rryske2001/modul-systemowy/plytki/wersja_ostateczna_wyswietlacz_pcf_v1/plots/LCD_PCF_v4__opis.pdf

# 47n C1 E J5

J12 | A⁰ | þÿZBcze LCD

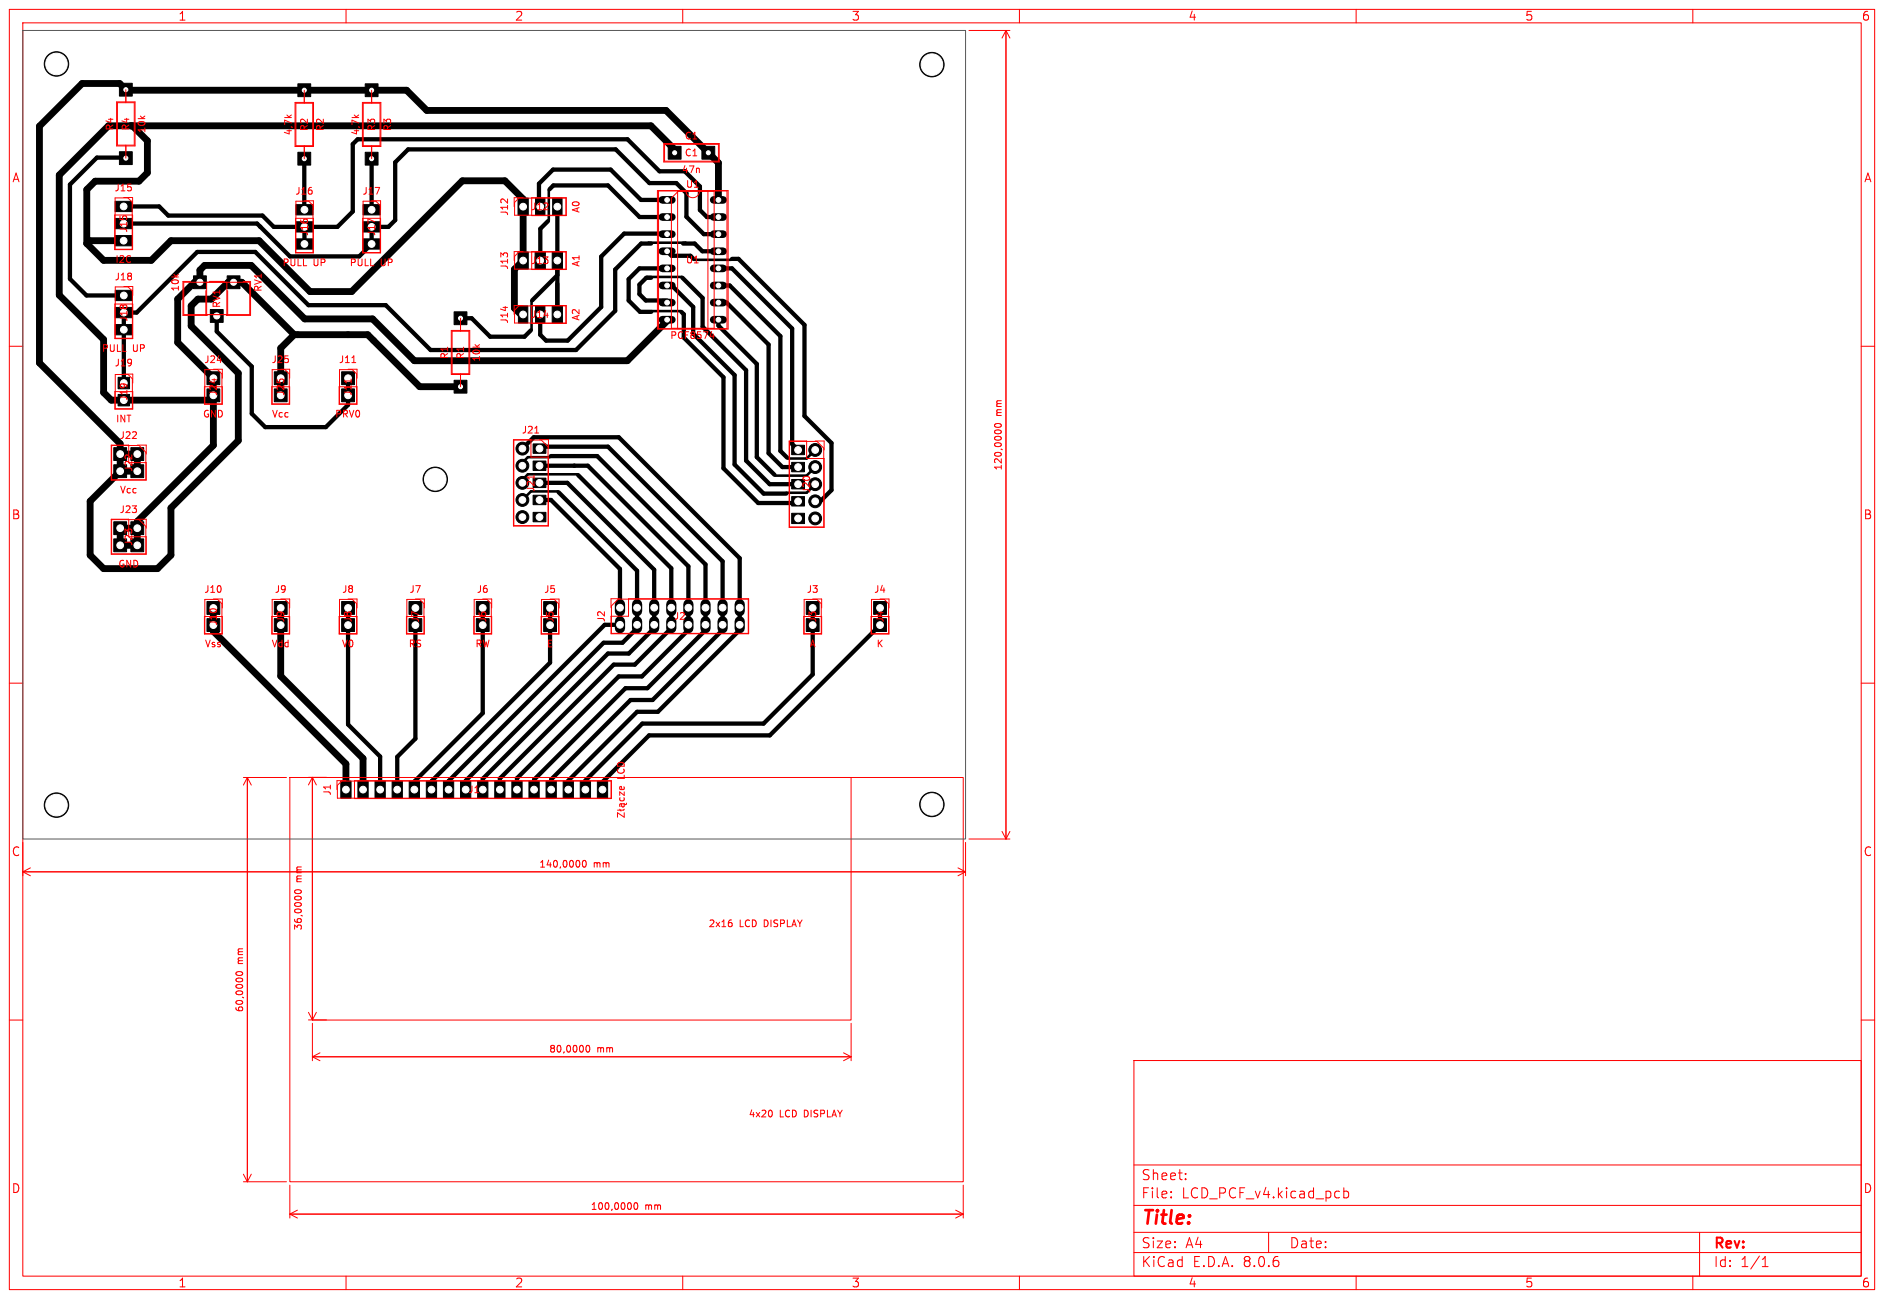
[picture p13: page 1]

Id: 1/1 Title: File: LCD_PCF_v4.kicad_pcb Sheet:
