rryske2001/modul-systemowy/plytki/wersja_ostateczna_wyswietlacz_pcf_v1/plots/wersja_ostateczna_wyswietlacz_pcf_v1_opis_sciezki.pdf

1 | 2 | 3 | 4 | 5 | 6

A

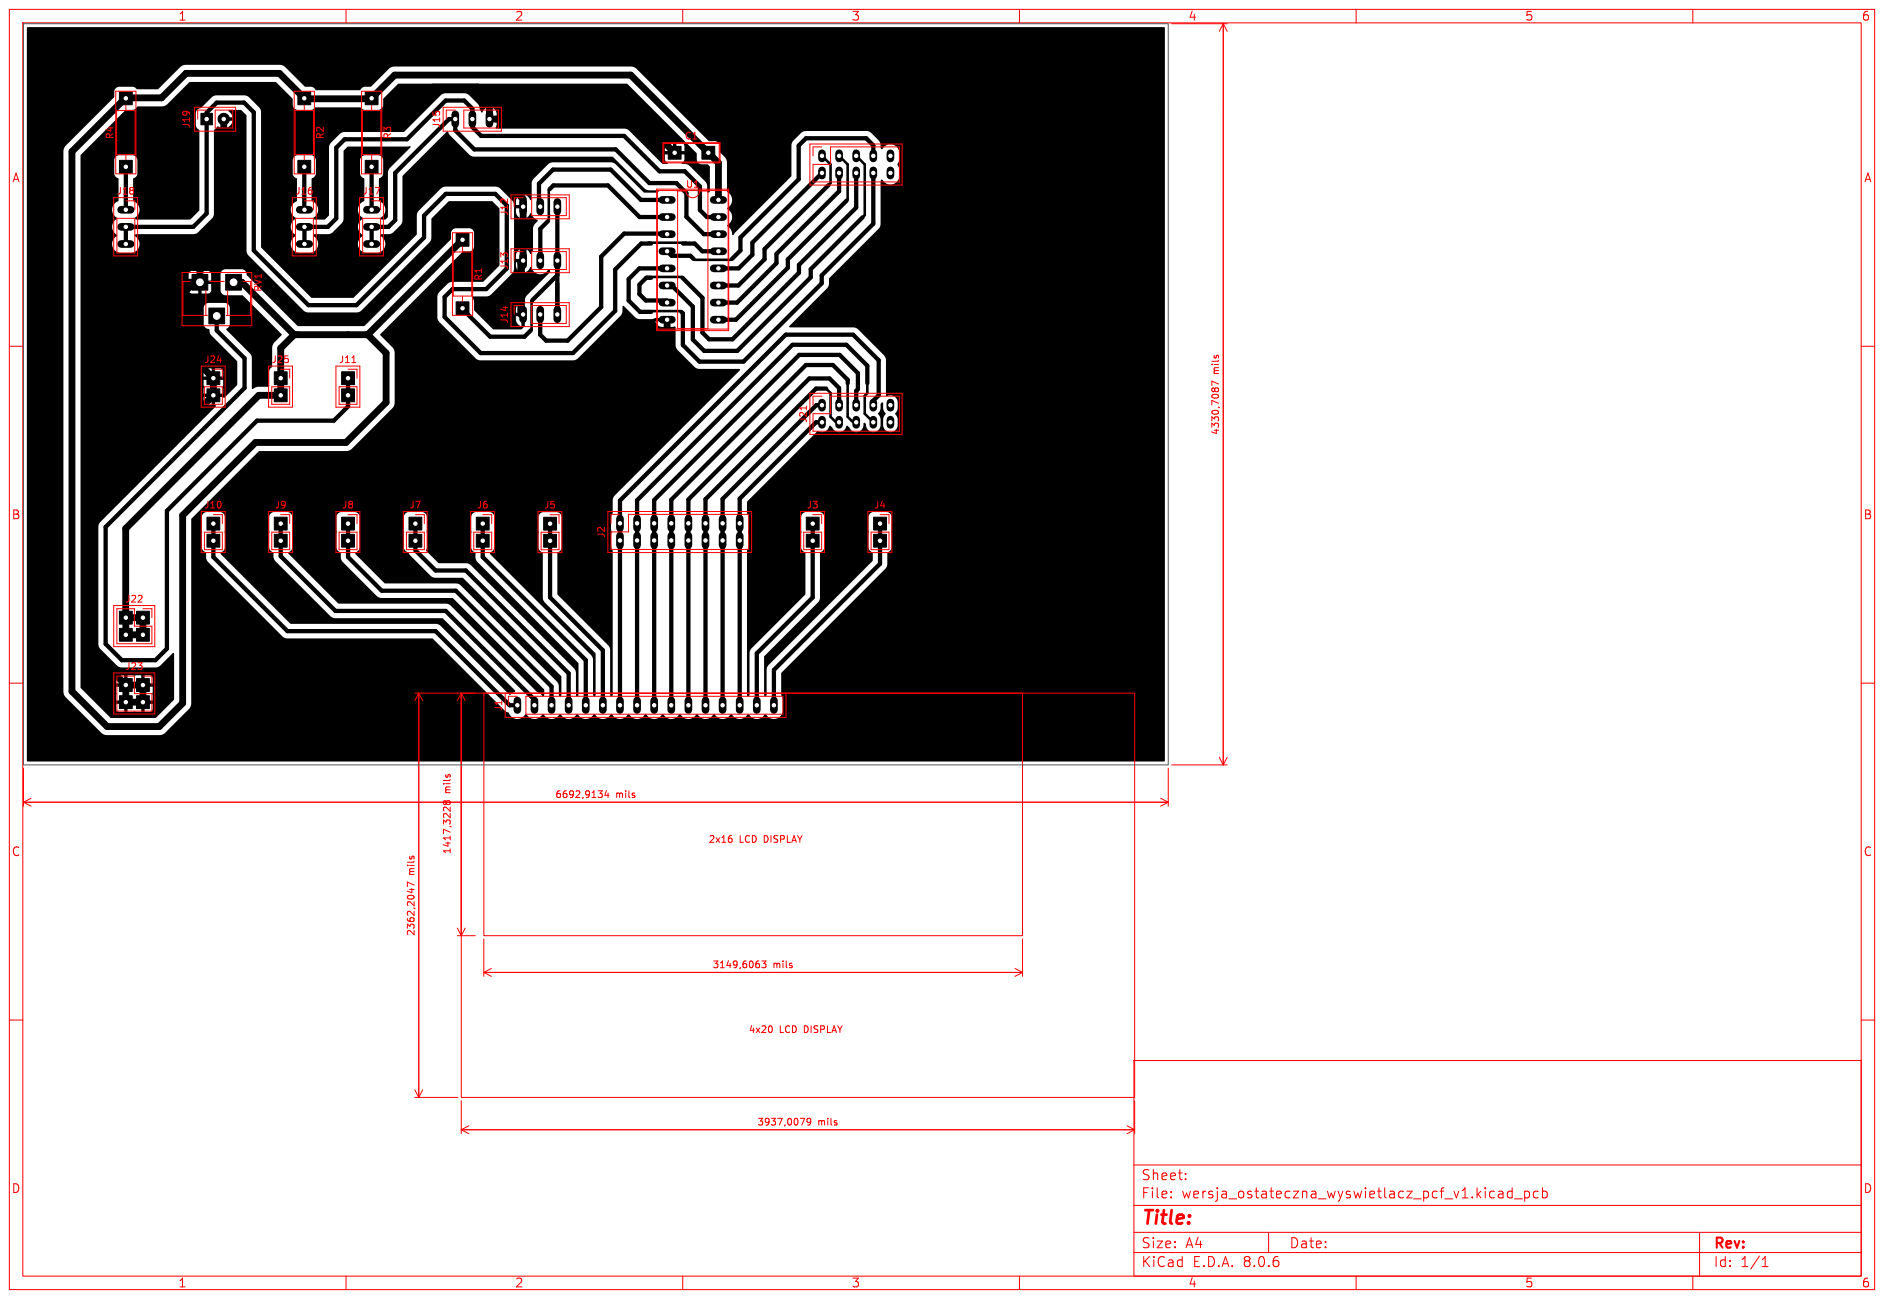
[picture p14: page 1]

Id: 1/1 Title: File: wersja_ostateczna_wyswietlacz_pcf_v1.kicad_pcb Sheet: ⁴x20 LCD DISPLAY
