rryske2001/modul-systemowy/plytki/wersja_ostateczna_wyswietlacz_pcf_v1/plots/wersja_ostateczna_wyswietlacz_pcf_v1_sciezki2.pdf

# J23 R⁴

J8 | R³ | R¹

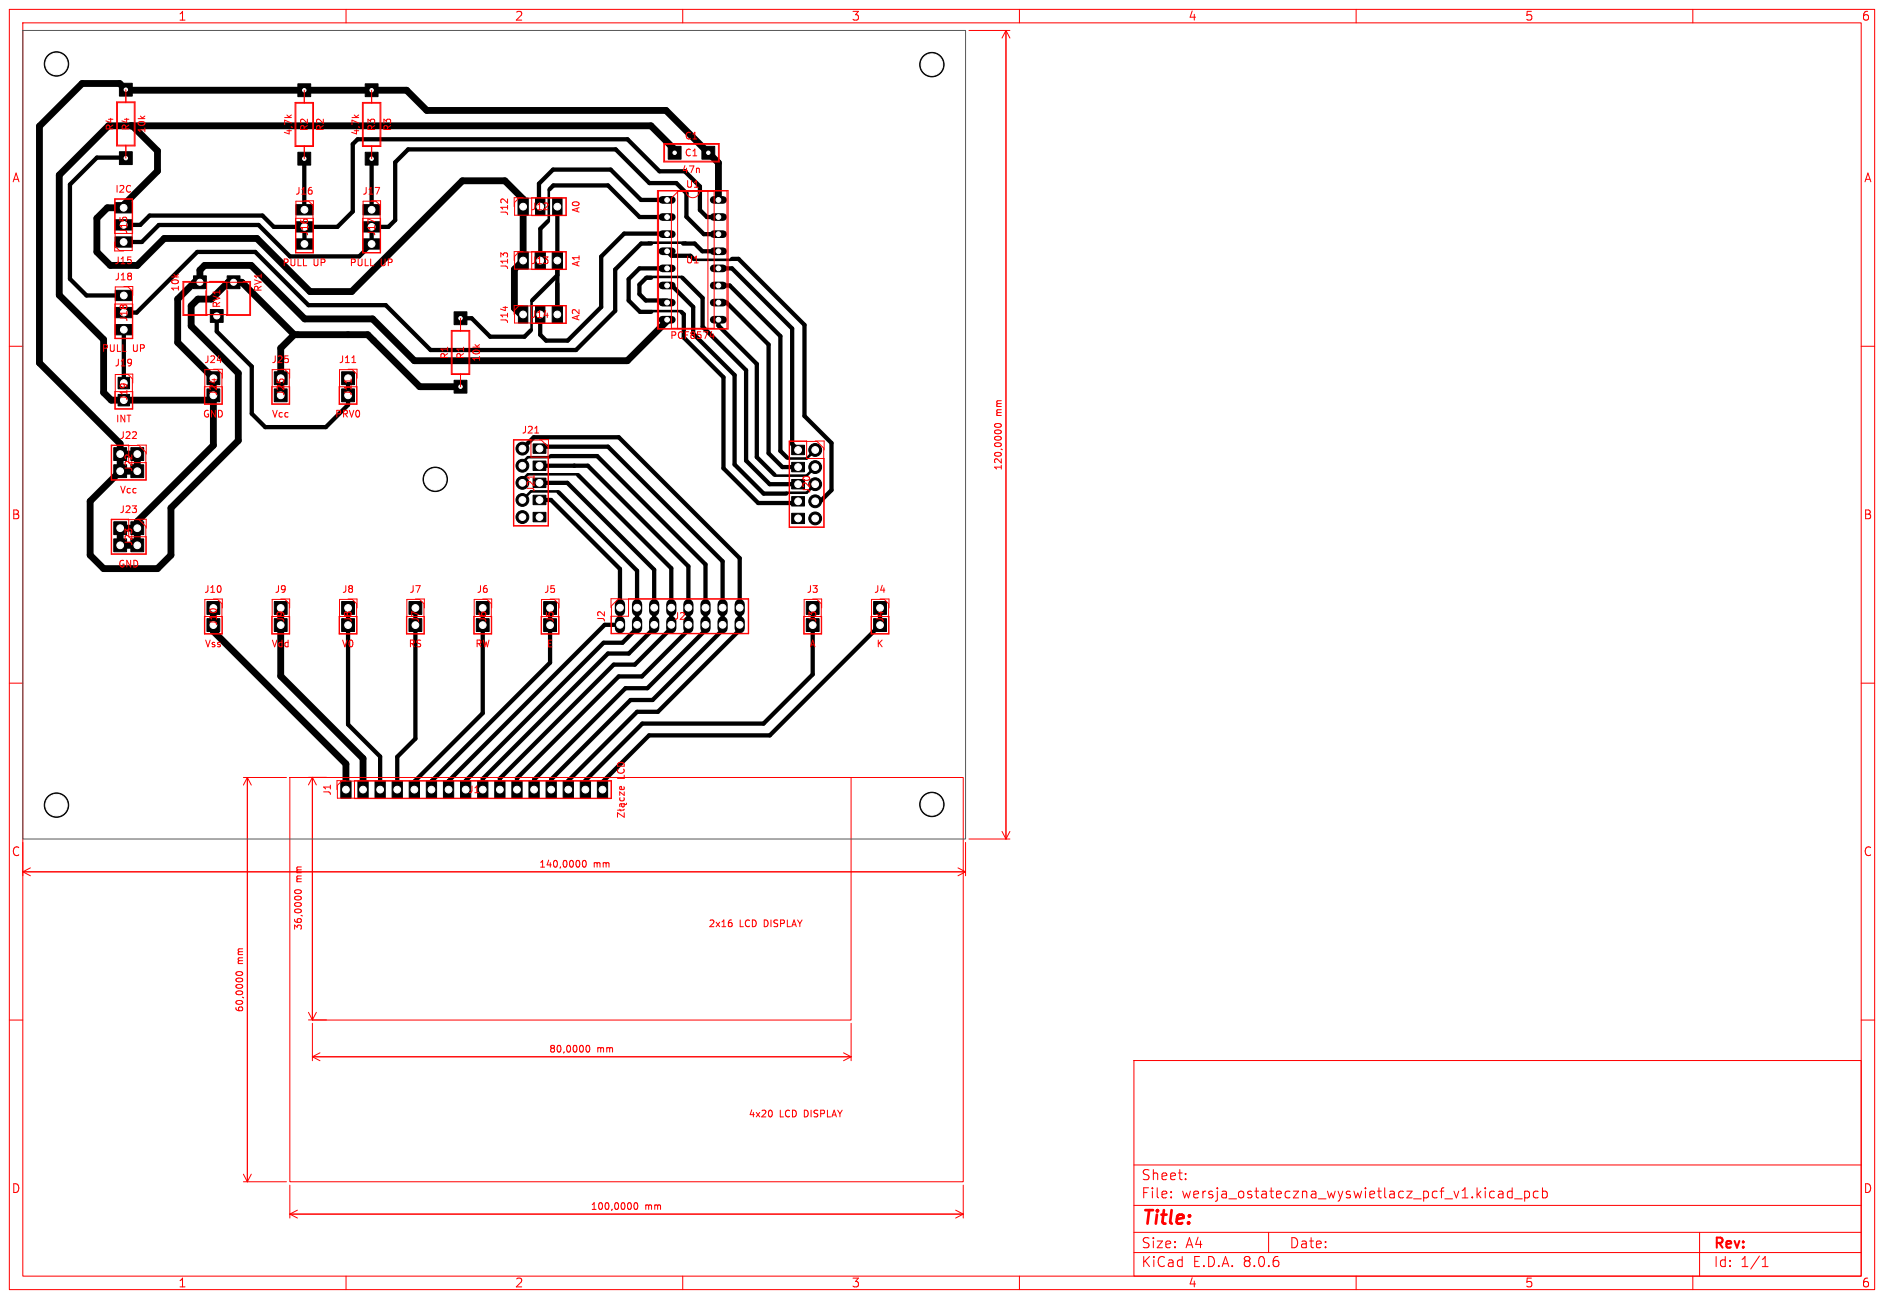
[picture p15: page 1]

Id: 1/1 Title: File: wersja_ostateczna_wyswietlacz_pcf_v1.kicad_pcb Sheet:
