rryske2001/modul-systemowy/plytki/Wersja_z_I2C_8bit_16x2_20x4_dwuwarstwowa/plots/Wersja_z_I2C_8bit_16x2_20x4_dwuwarstwowa_opis.pdf

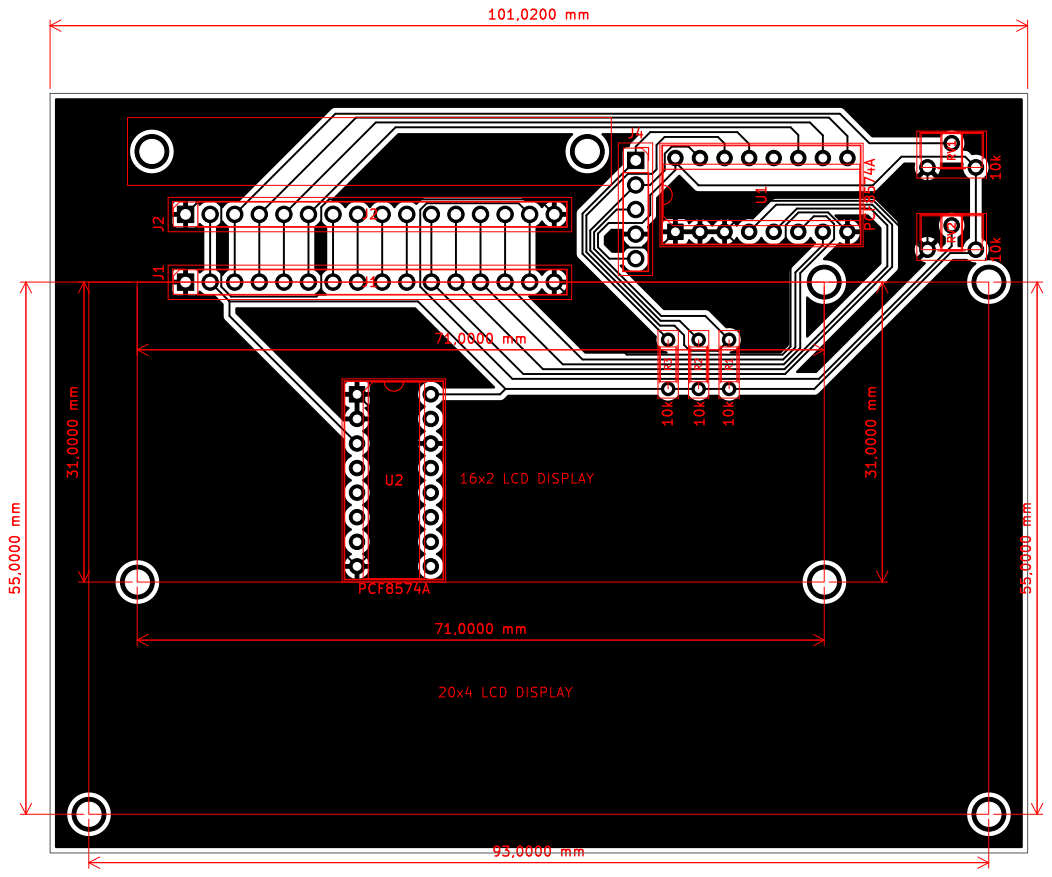
[picture p16: page 1]
D Date: KiCad; E.D.A. 8.0.6 Size: A4; Rev:; 10kRV² 10k R³; PCF8574A U¹ 10k R²; 10k R¹ J2 PCF8574A U2; 10kRV¹ 16x2 LCD DISPLAY; 20x4 LCD DISPLAY J1

Id: 1/1 Title: File: Wersja_z_I2C_8bit_16x2_20x4_dwuwarstwowa.kicad_pcb Sheet:

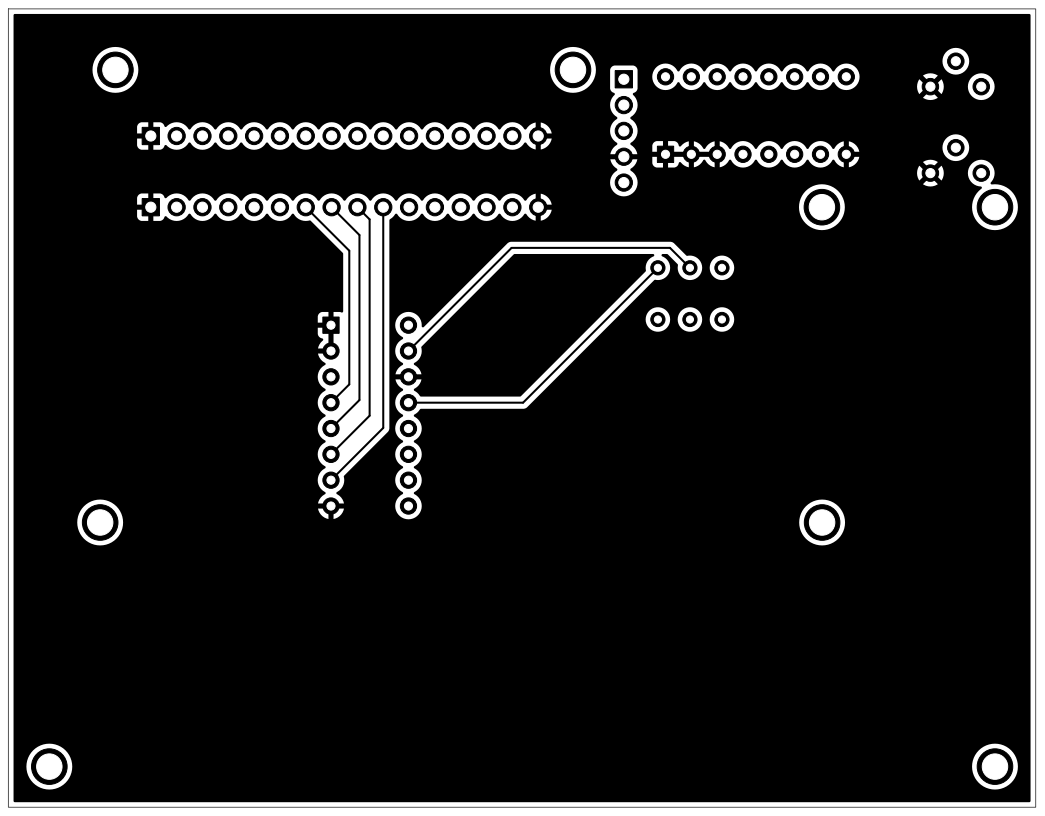
[picture p17: page 2]
D Date: KiCad; E.D.A. 8.0.6 Size: A4; Rev:

Id: 1/1 Title: File: Wersja_z_I2C_8bit_16x2_20x4_dwuwarstwowa.kicad_pcb Sheet:
