rryske2001/modul-systemowy/plytki/Wersja_z_I2C_8bit_16x2_20x4_dwuwarstwowa/plots/Wersja_z_I2C_8bit_16x2_20x4_dwuwarstwowa_sciezki.pdf

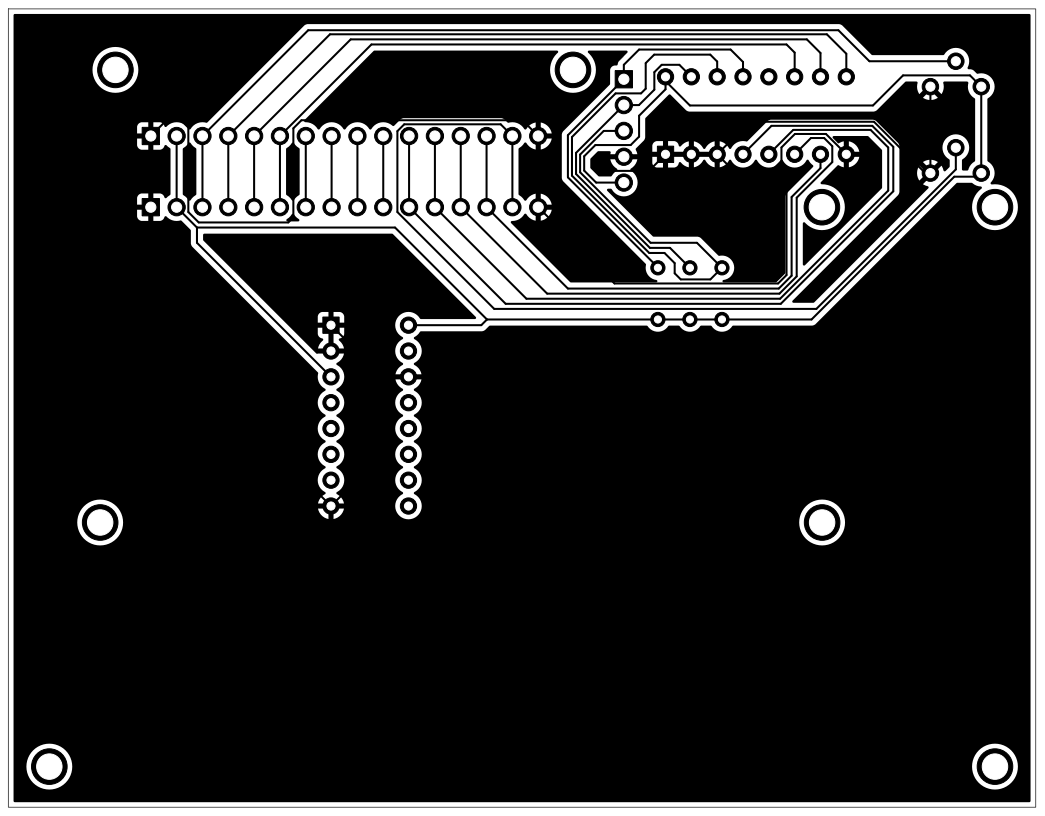
[picture p18: page 1]
D Date: KiCad; E.D.A. 8.0.6 Size: A4; Rev:

Id: 1/1 Title: File: Wersja_z_I2C_8bit_16x2_20x4_dwuwarstwowa.kicad_pcb Sheet:

D Date: KiCad; E.D.A. 8.0.6 Size: A4; Rev:

Id: 1/1 Title: File: Wersja_z_I2C_8bit_16x2_20x4_dwuwarstwowa.kicad_pcb Sheet:
