rryske2001/modul-systemowy/plytki/plytka_z_I2C-4bitowa_40x2v2/plytka_do_druku_v2/plots/plytka_do_druku_v2__opis.pdf

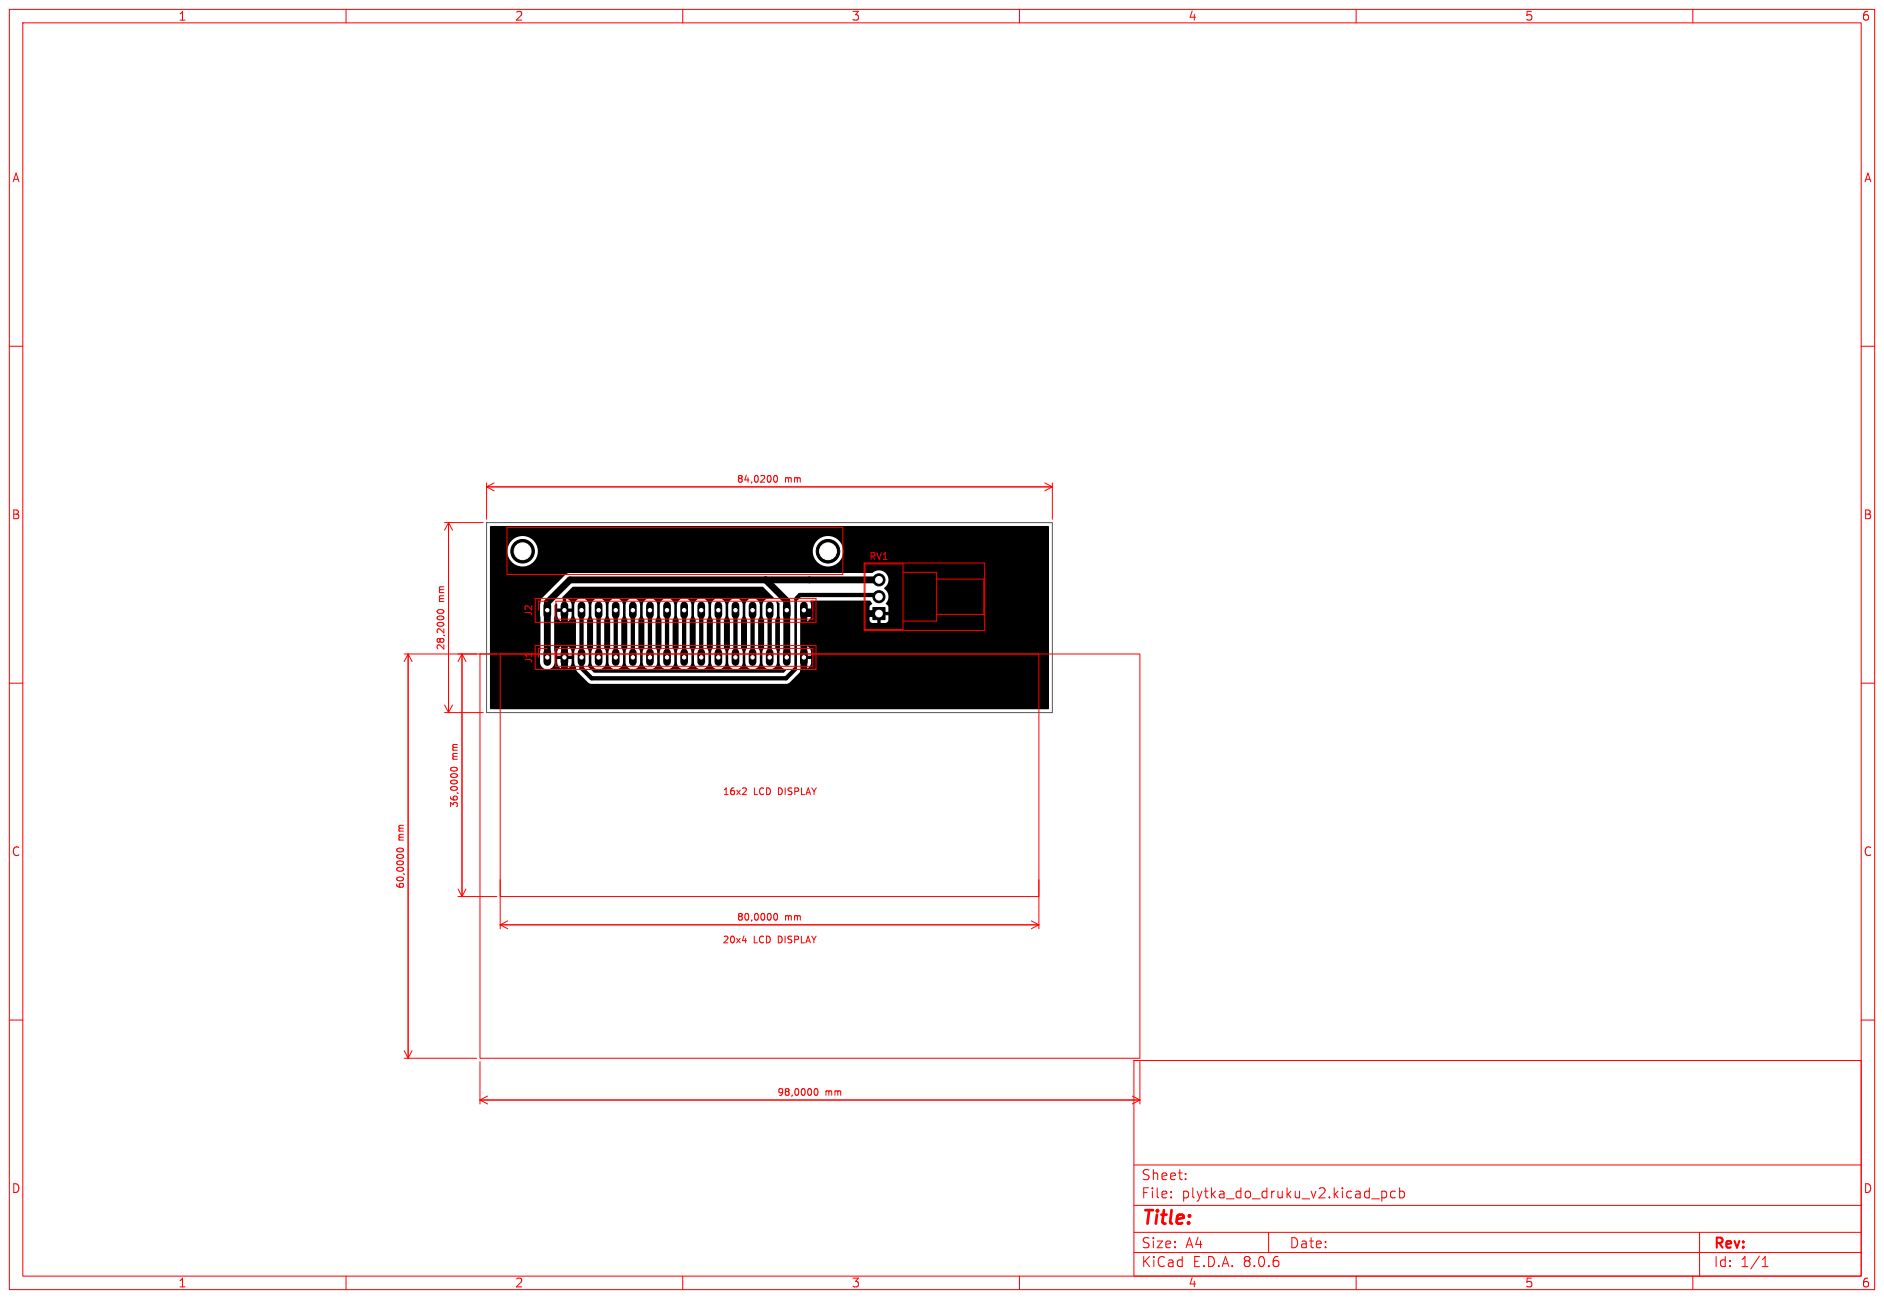
[picture p19: page 1]
D Date: KiCad; E.D.A. 8.0.6 Size: A4; Rev:; 16x2 LCD DISPLAY; 20x4 LCD DISPLAY J2 J1

Id: 1/1 Title: File: plytka_do_druku_v2.kicad_pcb Sheet:
