rryske2001/modul-systemowy/plytki/Wersja_z_I2C_8bit_16x2_20x4_dwuwarstwowa/plots/Wersja_z_I2C_8bit_16x2_20x4_dwuwarstwowa_opis (2).pdf

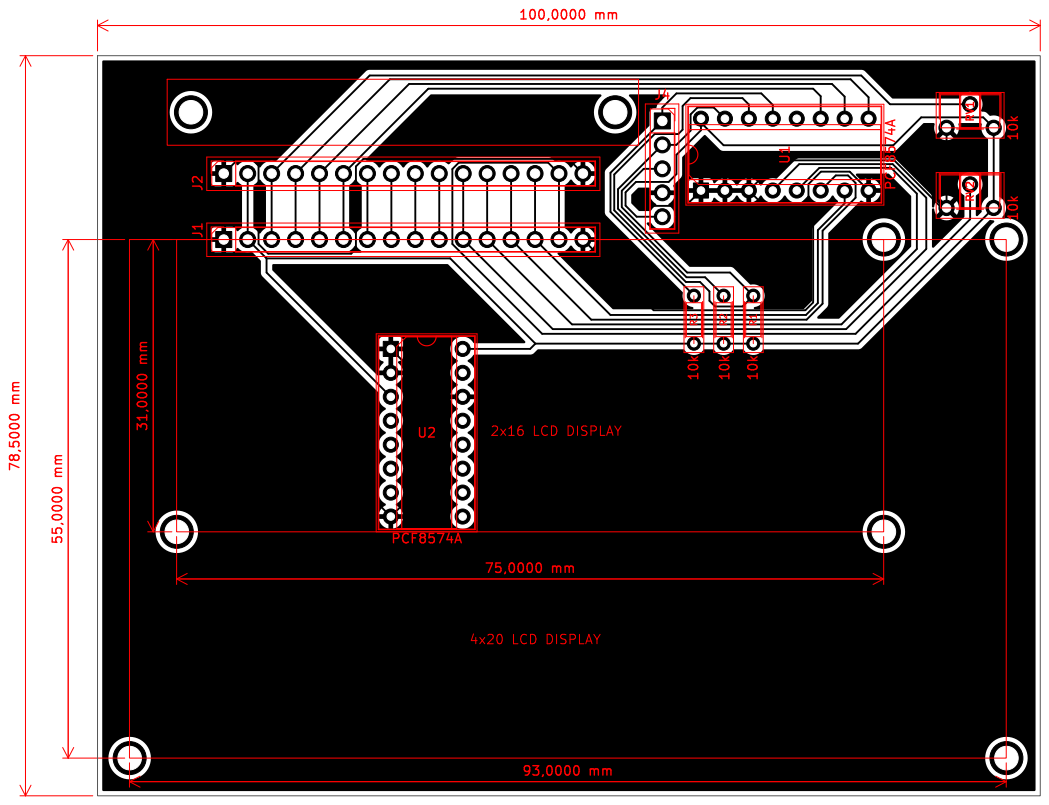
[picture p20: page 1]
D Date: KiCad; E.D.A. 8.0.6 Size: A4; Rev:; Id: 1/1 Title: File: Wersja_z_I2C_8bit_16x2_20x4_dwuwarstwowa.kicad_pcb Sheet: ¹⁰kRV² 10k R³; PCF8574A U¹ 10k R²; 10k R¹ PCF8574A U2; 10kRV¹ 2x16 LCD DISPLAY; 4x20 LCD DISPLAY J1

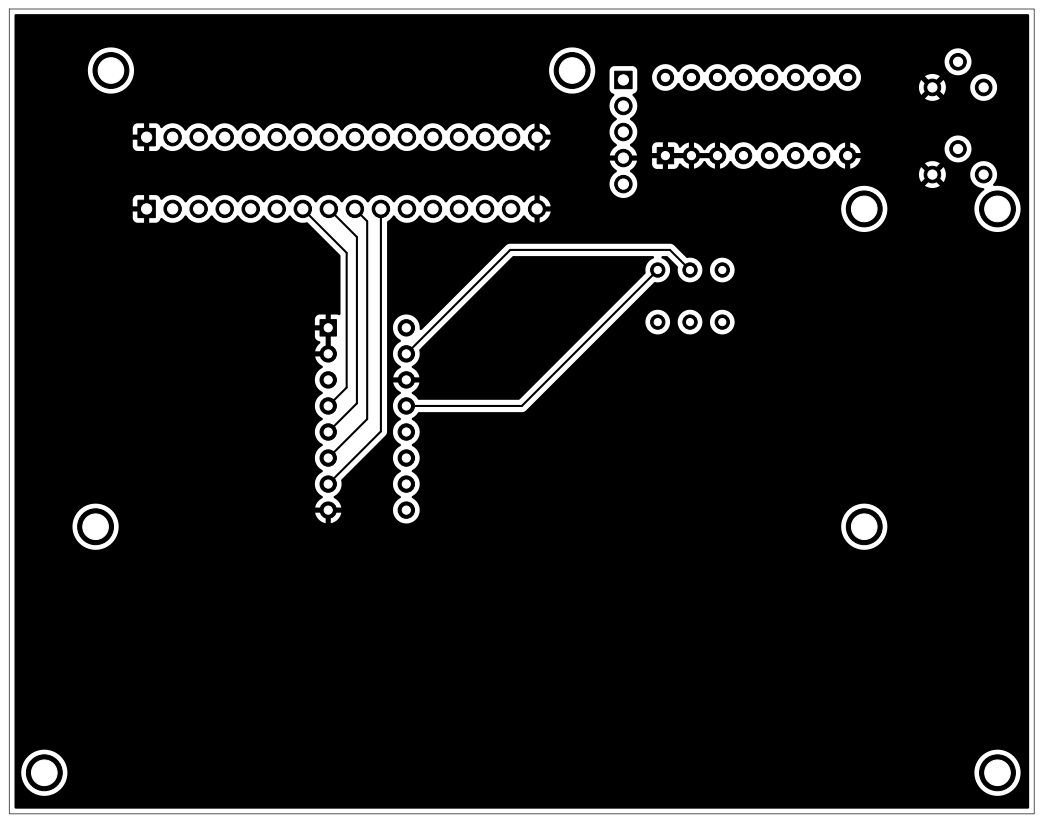
[picture p21: page 2]
D Date: KiCad; E.D.A. 8.0.6 Size: A4; Rev:

Id: 1/1 Title: File: Wersja_z_I2C_8bit_16x2_20x4_dwuwarstwowa.kicad_pcb Sheet:
